themuck/ZyklenAutomatik/Display/104-5.jpg

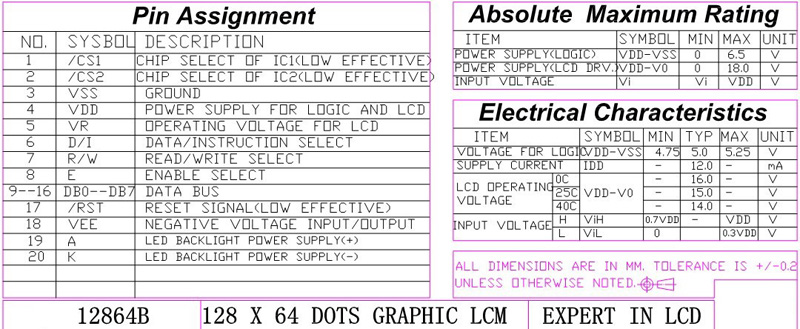
Display/104-5.jpg
